LX050724/HFLink/FPGA/src/top.v

`timescale 1 ns / 10 ps

module HFLink_TOP(
        input clk_osc

        ,inout MCU_SWDIO
        ,inout MCU_SWCLK
        // ,input reset

        ,output FLASH_SPI_CSN
        ,input FLASH_SPI_MISO
        ,output FLASH_SPI_MOSI
        ,output FLASH_SPI_CLK
        ,output FLASH_SPI_HOLDN
        ,output FLASH_SPI_WPN

        // 独立串口连接器
        ,output EXT_UART_TX
        ,input EXT_UART_RX

        // SWD/JTAG连接器端口
        ,output EXT_SWCLK_TCK_O
        ,output EXT_SWDIO_TMS_T
        ,output EXT_SWDIO_TMS_O
        ,input EXT_SWDIO_TMS_I
        ,input EXT_SWO_TDO_I
        ,output EXT_TDI_O
        ,input EXT_RTCK_I
        ,input EXT_SRST_I
        ,output EXT_SRST_O
        ,input EXT_TRST_I
        ,output EXT_TRST_O

        // RGB & PWRCTL
        ,output [3:0] GPIO

        // IIC
        ,inout IIC_SDA
        ,inout IIC_SCL

        // USB ULPI
        ,output usb_clk
        ,output usb_rstn
        ,inout [7:0] usb_ulpi_data
        ,input usb_ulpi_nxt
        ,input usb_ulpi_dir
        ,output usb_ulpi_stp
    );

    wire reset = 0;
    wire lock;
    wire clkout0;
    wire clkout1;
    wire clkout2;
    wire n_reset = !reset;
    wire m1_halt;
    wire [3:0] intr;
    assign ready_led = !m1_halt;

    assign FLASH_SPI_HOLDN = 1'd1;
    assign FLASH_SPI_WPN = 1'd1;

    wire [31:0] AHB1HRDATA;
    wire        AHB1HREADYOUT;
    wire [ 1:0] AHB1HRESP;
    wire [ 1:0] AHB1HTRANS;
    wire [ 2:0] AHB1HBURST;
    wire [ 3:0] AHB1HPROT;
    wire [ 2:0] AHB1HSIZE;
    wire        AHB1HWRITE;
    wire        AHB1HREADYMUX;
    wire [ 3:0] AHB1HMASTER;
    wire        AHB1HMASTLOCK;
    wire [31:0] AHB1HADDR;
    wire [31:0] AHB1HWDATA;
    wire        AHB1HSEL;
    wire        AHB1HCLK;
    wire        AHB1HRESET;

    wire [31:0] AHB2HRDATA;
    wire        AHB2HREADYOUT;
    wire [ 1:0] AHB2HRESP;
    wire [ 1:0] AHB2HTRANS;
    wire [ 2:0] AHB2HBURST;
    wire [ 3:0] AHB2HPROT;
    wire [ 2:0] AHB2HSIZE;
    wire        AHB2HWRITE;
    wire        AHB2HREADYMUX;
    wire [ 3:0] AHB2HMASTER;
    wire        AHB2HMASTLOCK;
    wire [31:0] AHB2HADDR;
    wire [31:0] AHB2HWDATA;
    wire        AHB2HSEL;
    wire        AHB2HCLK;
    wire        AHB2HRESET;

    wire [31:0] APB1PADDR;
    wire        APB1PENABLE;
    wire        APB1PWRITE;
    wire [ 3:0] APB1PSTRB;
    wire [ 2:0] APB1PPROT;
    wire [31:0] APB1PWDATA;
    wire        APB1PSEL;
    wire [31:0] APB1PRDATA;
    wire        APB1PREADY;
    wire        APB1PSLVERR;
    wire        APB1PCLK;
    wire        APB1PRESET;

    Gowin_PLL main_pll(
                  .lock(lock), //output lock
                  .clkout0(clkout0), //output clkout0
                  .clkout1(clkout1), //output clkout1
                  .clkout2(clkout2), //output clkout2
                  .clkin(clk_osc), //input clkin
                  .mdclk(clk_osc)
                  //   .reset(reset) //input reset
              );

    wire cm_nreset = n_reset & lock;

    wire MCU_SPI_MOSI;
    wire MCU_SPI_MISO;
    wire MCU_SPI_CLK;
    wire MCU_SPI_CSN;

    Gowin_EMPU_M1_Top Cortex_M1 (
                          //.LOCKUP(lockup), //output LOCKUP
                          .HALTED(m1_halt), //output HALTED
                          .JTAG_7(MCU_SWDIO), //inout JTAG_7
                          .JTAG_9(MCU_SWCLK), //inout JTAG_9
                          .HCLK(clkout0), //input HCLK
                          .hwRstn(cm_nreset), //input hwRstn


                          // AHB1 0x80000000
                          .AHB1HRDATA(AHB1HRDATA), //input [31:0] AHB1HRDATA
                          .AHB1HREADYOUT(AHB1HREADYOUT), //input AHB1HREADYOUT
                          .AHB1HRESP(AHB1HRESP), //input [1:0] AHB1HRESP
                          .AHB1HTRANS(AHB1HTRANS), //output [1:0] AHB1HTRANS
                          .AHB1HBURST(AHB1HBURST), //output [2:0] AHB1HBURST
                          .AHB1HPROT(AHB1HPROT), //output [3:0] AHB1HPROT
                          .AHB1HSIZE(AHB1HSIZE), //output [2:0] AHB1HSIZE
                          .AHB1HWRITE(AHB1HWRITE), //output AHB1HWRITE
                          .AHB1HREADYMUX(AHB1HREADYMUX), //output AHB1HREADYMUX
                          .AHB1HMASTER(AHB1HMASTER), //output [3:0] AHB1HMASTER
                          .AHB1HMASTLOCK(AHB1HMASTLOCK), //output AHB1HMASTLOCK
                          .AHB1HADDR(AHB1HADDR), //output [31:0] AHB1HADDR
                          .AHB1HWDATA(AHB1HWDATA), //output [31:0] AHB1HWDATA
                          .AHB1HSEL(AHB1HSEL), //output AHB1HSEL
                          .AHB1HCLK(AHB1HCLK), //output AHB1HCLK
                          .AHB1HRESET(AHB1HRESET), //output AHB1HRESET

                          // AHB2 0x81000000
                          .AHB2HRDATA(AHB2HRDATA), //input [31:0] AHB2HRDATA
                          .AHB2HREADYOUT(AHB2HREADYOUT), //input AHB2HREADYOUT
                          .AHB2HRESP(AHB2HRESP), //input [1:0] AHB2HRESP
                          .AHB2HTRANS(AHB2HTRANS), //output [1:0] AHB2HTRANS
                          .AHB2HBURST(AHB2HBURST), //output [2:0] AHB2HBURST
                          .AHB2HPROT(AHB2HPROT), //output [3:0] AHB2HPROT
                          .AHB2HSIZE(AHB2HSIZE), //output [2:0] AHB2HSIZE
                          .AHB2HWRITE(AHB2HWRITE), //output AHB2HWRITE
                          .AHB2HREADYMUX(AHB2HREADYMUX), //output AHB2HREADYMUX
                          .AHB2HMASTER(AHB2HMASTER), //output [3:0] AHB2HMASTER
                          .AHB2HMASTLOCK(AHB2HMASTLOCK), //output AHB2HMASTLOCK
                          .AHB2HADDR(AHB2HADDR), //output [31:0] AHB2HADDR
                          .AHB2HWDATA(AHB2HWDATA), //output [31:0] AHB2HWDATA
                          .AHB2HSEL(AHB2HSEL), //output AHB2HSEL
                          .AHB2HCLK(AHB2HCLK), //output AHB2HCLK
                          .AHB2HRESET(AHB2HRESET), //output AHB2HRESET

                          // APB1 0x60000000
                          .APB1PADDR(APB1PADDR), //output [31:0] APB1PADDR
                          .APB1PENABLE(APB1PENABLE), //output APB1PENABLE
                          .APB1PWRITE(APB1PWRITE), //output APB1PWRITE
                          .APB1PSTRB(APB1PSTRB), //output [3:0] APB1PSTRB
                          .APB1PPROT(APB1PPROT), //output [2:0] APB1PPROT
                          .APB1PWDATA(APB1PWDATA), //output [31:0] APB1PWDATA
                          .APB1PSEL(APB1PSEL), //output APB1PSEL
                          .APB1PRDATA(APB1PRDATA), //input [31:0] APB1PRDATA
                          .APB1PREADY(APB1PREADY), //input APB1PREADY
                          .APB1PSLVERR(APB1PSLVERR), //input APB1PSLVERR
                          .APB1PCLK(APB1PCLK), //output APB1PCLK
                          .APB1PRESET(APB1PRESET), //output APB1PRESET

                          // SPI
                          .MOSI(MCU_SPI_MOSI), //output MOSI
                          .MISO(MCU_SPI_MISO), //input MISO
                          .SCLK(MCU_SPI_CLK), //output SCLK
                          .NSS(MCU_SPI_CSN), //output NSS

                          // IIC
                          .SDA(IIC_SDA),
                          .SCL(IIC_SCL),

                          .EXTINT(intr) //input [3:0] EXTINT
                      );

    wire [7:0] usb_ulpi_data_i;
    wire [7:0] usb_ulpi_data_o;

    wire winusb_out_tready;
    wire winusb_out_tvalid;
    wire [7:0] winusb_out_tdata;
    wire cdc_in_tvalid;
    wire [7:0] cdc_in_tdata;
    wire cdc_out_tready;
    wire cdc_out_tvalid;
    wire [7:0] cdc_out_tdata;

    wire [3:0] ext_usb_endpt;
    wire ext_usb_txact;
    wire ext_usb_txpop;
    wire ext_usb_txpktfin;
    wire ext_usb_txcork;
    wire [7:0] ext_usb_txdata;
    wire [11:0] ext_usb_txlen;
    wire [7:0] ext_usb_rxdat;
    wire ext_usb_rxval;
    wire ext_usb_rxrdy;
    wire ext_usb_rxact;
    wire ext_usb_rxpktval;


    AHB_USBDevice u_usb0 (
                      .hclk(AHB1HCLK),
                      .hresetn(AHB1HRESET),
                      .hsels(AHB1HSEL),
                      .haddrs(AHB1HADDR[11:0]),
                      .htranss(AHB1HTRANS),
                      .hsizes(AHB1HSIZE),
                      .hwrites(AHB1HWRITE),
                      .hreadys(AHB1HREADYMUX),
                      .hwdatas(AHB1HWDATA),
                      .hreadyouts(AHB1HREADYOUT),
                      .hresps(AHB1HRESP[0]),
                      .hrdatas(AHB1HRDATA),
                      .intr(intr[0]),
                      .usb_ulpi_data_i(usb_ulpi_data_i),
                      .usb_ulpi_data_o(usb_ulpi_data_o),
                      .usb_ulpi_data(usb_ulpi_data),
                      .usb_ulpi_nxt(usb_ulpi_nxt),
                      .usb_ulpi_dir(usb_ulpi_dir),
                      .usb_ulpi_stp(usb_ulpi_stp),
                      .usb_nrst(usb_rstn),

                      .ext_usb_endpt(ext_usb_endpt),
                      .ext_usb_txact(ext_usb_txact),
                      .ext_usb_txpop(ext_usb_txpop),
                      .ext_usb_txpktfin(ext_usb_txpktfin),
                      .ext_usb_txcork(ext_usb_txcork),
                      .ext_usb_txdata(ext_usb_txdata),
                      .ext_usb_txlen(ext_usb_txlen),
                      .ext_usb_rxdat(ext_usb_rxdat),
                      .ext_usb_rxval(ext_usb_rxval),
                      .ext_usb_rxrdy(ext_usb_rxrdy),
                      .ext_usb_rxact(ext_usb_rxact),
                      .ext_usb_rxpktval(ext_usb_rxpktval),

                      .cdc_in_tvalid(cdc_in_tvalid),
                      .cdc_in_tdata(cdc_in_tdata),
                      .cdc_out_tready(cdc_out_tready),
                      .cdc_out_tvalid(cdc_out_tvalid),
                      .cdc_out_tdata(cdc_out_tdata)
                  );
    assign usb_clk = AHB1HCLK;

    genvar i;
    generate
        for(i = 0; i < 8; i = i + 1) begin: io_genfor
            IOBUF usb_data_io_u(
                      .O(usb_ulpi_data_i[i]),
                      .I(usb_ulpi_data_o[i]),
                      .IO(usb_ulpi_data[i]),
                      .OEN(usb_ulpi_dir)
                  );
        end
    endgenerate

    wire LOC_UART_TX;
    wire LOC_UART_RX;

    // ── UART ↔ USB CDC 桥接 (DAP_USB_Receiver / DAP_USB_Transfer) ──
    wire        cdc_txcork, cdc_rxrdy;
    wire [7:0]  cdc_txdata;
    wire [11:0] cdc_txlen;
    wire        uart_tx_tvalid;
    wire        uart_tx_tready;
    wire [7:0]  uart_tx_tdata;
    wire        uart_rx_tvalid;
    wire [7:0]  uart_rx_tdata;
    wire        uart_rx_fifo_clear;
    wire        uart_rx_fifo_clear_done;
    wire        uart_tx_fifo_clear;
    wire        uart_tx_fifo_clear_done;

    // CDC OUT (EP4, host→device): USB RX → AXIS → UART TX
    DAP_USB_Receiver #(
        .P_ENDPOINT(4'd4),
        .FIFO_DEPTH(1024),
        .FIFO_BUFFER_LEN(512)
    ) cdc_usb_receiver (
        .clk(AHB1HCLK),
        .resetn(AHB1HRESET),

        .clear_data(uart_tx_fifo_clear),
        .clear_done(uart_tx_fifo_clear_done),

        .usb_endpt(ext_usb_endpt),
        .usb_rxval(ext_usb_rxval),
        .usb_rxdat(ext_usb_rxdat),
        .usb_rxpktval(ext_usb_rxpktval),
        .usb_rxact(ext_usb_rxact),
        .usb_rxrdy(cdc_rxrdy),

        .fifo_full(),
        .fifo_empty(),

        .axis_tvaild(uart_tx_tvalid),
        .axis_tdata(uart_tx_tdata),
        .axis_tready(uart_tx_tready)
    );

    // UART RX → AXIS → USB TX → CDC IN (EP3, device→host)
    DAP_USB_Transfer #(
        .P_ENDPOINT(4'd3),
        .FIFO_DEPTH(1024),
        .FIFO_BUFFER_LEN(512)
    ) cdc_usb_transfer (
        .clk(AHB1HCLK),
        .resetn(AHB1HRESET),

        .clear_data(uart_rx_fifo_clear),
        .clear_done(uart_rx_fifo_clear_done),

        .in_tvalid(uart_rx_tvalid),
        .in_tready(),
        .in_tdata(uart_rx_tdata),

        .fifo_size(),

        .usb_endpt(ext_usb_endpt),
        .usb_txact(ext_usb_txact),
        .usb_txpop(ext_usb_txpop),
        .usb_txpktfin(ext_usb_txpktfin),
        .usb_txcork(cdc_txcork),
        .usb_txdata(cdc_txdata),
        .usb_txlen(cdc_txlen)
    );

    // ── APB_Stream_UART (保留 APB 配置 + UART 物理层) ──
    APB_Stream_UART apb_stream_uart(
                        // APB
                        .PCLK(APB1PCLK),
                        .PWRITE(APB1PWRITE),
                        .PSEL(APB1PSEL),
                        .PENABLE(APB1PENABLE),
                        .PADDR(APB1PADDR),
                        .PSTRB(APB1PSTRB),
                        .PWDATA(APB1PWDATA),
                        .PRDATA(APB1PRDATA),
                        .PREADY(APB1PREADY),
                        .PRESETn(APB1PRESET),

                        .rx_fifo_clear(uart_rx_fifo_clear),
                        .rx_fifo_clear_done(uart_rx_fifo_clear_done),
                        .tx_fifo_clear(uart_tx_fifo_clear),
                        .tx_fifo_clear_done(uart_tx_fifo_clear_done),

                        // Data Stream (经 DAP 模块桥接)
                        .tx_tvalid(uart_tx_tvalid),
                        .tx_tready(uart_tx_tready),
                        .tx_tdata(uart_tx_tdata),
                        .rx_tvalid(uart_rx_tvalid),
                        .rx_tdata(uart_rx_tdata),

                        // UART IO
                        .UART_TX(LOC_UART_TX),
                        .UART_RX(LOC_UART_RX)
                    );

    // ── 原内部 CDC 路径 (usb_fifo) 已移除，端口接地 ──
    assign cdc_in_tvalid = 1'b0;
    assign cdc_in_tdata  = 8'd0;
    assign cdc_out_tready = 1'b0;

    wire LOC_SPI_MUX;
    wire LOC_SPI_MISO;

    // ── USB TX/RX 多路复用: DAP_Controller ↔ CDC 桥接 ──
    wire        dap_txcork, dap_rxrdy;
    wire [7:0]  dap_txdata;
    wire [11:0] dap_txlen;

    DAP_Controller dap_controller_inst(
                       .hclk(AHB2HCLK),
                       .hresetn(AHB2HRESET),
                       .hsels(AHB2HSEL),
                       .haddrs(AHB2HADDR[11:0]),
                       .htranss(AHB2HTRANS),
                       .hsizes(AHB2HSIZE),
                       .hwrites(AHB2HWRITE),
                       .hreadys(AHB2HREADYMUX),
                       .hwdatas(AHB2HWDATA),
                       .hreadyouts(AHB2HREADYOUT),
                       .hresps(AHB2HRESP[0]),
                       .hrdatas(AHB2HRDATA),

                       .sclk(clkout1),
                       .clk_200M(clkout2),

                       .usb_endpt(ext_usb_endpt),
                       .usb_txact(ext_usb_txact),
                       .usb_txpop(ext_usb_txpop),
                       .usb_txpktfin(ext_usb_txpktfin),
                       .usb_txcork(dap_txcork),
                       .usb_txdata(dap_txdata),
                       .usb_txlen(dap_txlen),
                       .usb_rxdat(ext_usb_rxdat),
                       .usb_rxval(ext_usb_rxval),
                       .usb_rxrdy(dap_rxrdy),
                       .usb_rxact(ext_usb_rxact),
                       .usb_rxpktval(ext_usb_rxpktval),

                       .intr(intr[1]),

                       .EXT_SWCLK_TCK_O(EXT_SWCLK_TCK_O),
                       .EXT_SWDIO_TMS_T(EXT_SWDIO_TMS_T),
                       .EXT_SWDIO_TMS_O(EXT_SWDIO_TMS_O),
                       .EXT_SWDIO_TMS_I(EXT_SWDIO_TMS_I),
                       .EXT_SWO_TDO_I(EXT_SWO_TDO_I),
                       .EXT_TDI_O(EXT_TDI_O),
                       .EXT_RTCK_I(EXT_RTCK_I),
                       .EXT_SRST_I(EXT_SRST_I),
                       .EXT_SRST_O(EXT_SRST_O),
                       .EXT_TRST_I(EXT_TRST_I),
                       .EXT_TRST_O(EXT_TRST_O),
                       .EXT_UART_TX(EXT_UART_TX),
                       .EXT_UART_RX(EXT_UART_RX),

                       .LOC_UART_TX(LOC_UART_TX),
                       .LOC_UART_RX(LOC_UART_RX),

                       .LOC_SPI_CSN(MCU_SPI_CSN),
                       .LOC_SPI_MISO(LOC_SPI_MISO),
                       .LOC_SPI_MOSI(MCU_SPI_MOSI),
                       .LOC_SPI_CLK(MCU_SPI_CLK),
                       .LOC_SPI_MUX(LOC_SPI_MUX),
                       .DAP_GPIO(GPIO)
                   );

    // ── 外部 USB TX/RX 多路复用 ──
    assign ext_usb_txcork = (ext_usb_endpt == 4'd3) ? cdc_txcork : dap_txcork;
    assign ext_usb_txdata = (ext_usb_endpt == 4'd3) ? cdc_txdata : dap_txdata;
    assign ext_usb_txlen  = (ext_usb_endpt == 4'd3) ? cdc_txlen  : dap_txlen;
    assign ext_usb_rxrdy  = (ext_usb_endpt == 4'd4) ? cdc_rxrdy : dap_rxrdy;

    assign MCU_SPI_MISO = LOC_SPI_MUX ? LOC_SPI_MISO : FLASH_SPI_MISO;
    assign FLASH_SPI_CSN = LOC_SPI_MUX ? 1'd1 : MCU_SPI_CSN;
    assign FLASH_SPI_MOSI = LOC_SPI_MUX ? 1'd0 : MCU_SPI_MOSI;
    assign FLASH_SPI_CLK = LOC_SPI_MUX ? 1'd0 : MCU_SPI_CLK;
endmodule
