LX050724/HFLink/FPGA/src/USB_desc.v

`timescale 1 ns / 10 ps

module USB_DESC#(
        parameter ADDRWIDTH = 12,
        parameter [ADDRWIDTH-1:0] BASE_ADDR = 0
    ) (
        input clk,
        input resetn,
        input usbrst,

        // AHB MEM接口
        input ahb_write_en,
        input ahb_read_en,
        input [ADDRWIDTH-1:0] ahb_addr,
        output reg [31:0] ahb_rdata,
        input [31:0] ahb_wdata,
        input [3:0] ahb_byte_strobe,

        output [7:0] txdat,
        output reg txval,
        output reg [11:0] txdat_len,
        input txpop,
        input txact,
        input [7:0] rxdat,
        input rxval,
        output reg rxrdy,
        input rxact,
        input setup,
        input [3:0] endpt_sel,

        input [15:0] descrom_raddr,
        input [7:0] desc_index,
        input [7:0] desc_type,
        output [7:0] descrom_rdata,
        output [15:0] desc_dev_addr,
        output [15:0] desc_dev_len,
        output [15:0] desc_qual_addr,
        output [15:0] desc_qual_len,
        output [15:0] desc_fscfg_addr,
        output [15:0] desc_fscfg_len,
        output [15:0] desc_hscfg_addr,
        output [15:0] desc_hscfg_len,
        output [15:0] desc_oscfg_addr,
        output [15:0] desc_hidrpt_addr,
        output [15:0] desc_hidrpt_len,
        output [15:0] desc_bos_addr,
        output [15:0] desc_bos_len,
        output [15:0] desc_strlang_addr,
        output [15:0] desc_strvendor_addr,
        output [15:0] desc_strvendor_len,
        output [15:0] desc_strproduct_addr,
        output [15:0] desc_strproduct_len,
        output [15:0] desc_strserial_addr,
        output [15:0] desc_strserial_len,
        output desc_have_strings,

        output reg intr
    );

    localparam [ADDRWIDTH-1:0] USB_SETUP_DATA_ADDR  = 12'h000 + BASE_ADDR; // 8B RO
    localparam [ADDRWIDTH-1:0] CDC_LINE_CODE_ADDR   = 12'h008 + BASE_ADDR; // 6+2B RO
    localparam [ADDRWIDTH-1:0] SERIAL_DESC_ADDR     = 12'h010 + BASE_ADDR; // 68B RW


    reg [7:0] desc_rom [0:503];

    assign desc_dev_addr = 16'd10;
    assign desc_dev_len = 16'd18;
    assign desc_qual_addr = 16'd0;
    assign desc_qual_len = 16'd10;
    assign desc_fscfg_addr = 16'd133;
    assign desc_fscfg_len = 16'd105;
    assign desc_hscfg_addr = 16'd28;
    assign desc_hscfg_len = 16'd105;
    assign desc_oscfg_addr = 16'd238;
    assign desc_hidrpt_addr = 16'd0;
    assign desc_hidrpt_len = 16'd0;
    assign desc_bos_addr = 16'd409;
    assign desc_bos_len = 16'd33;
    assign desc_strlang_addr = 16'd442;
    assign desc_strvendor_addr = 16'd446;
    assign desc_strvendor_len = 16'd14;
    assign desc_strproduct_addr = 16'd460;
    assign desc_strproduct_len = 16'd44;
    assign desc_strserial_addr = 16'h8000;
    assign desc_strserial_len = 16'd66;
    assign desc_have_strings = 1'd1;

    localparam [15:0] desc_winusb_addr = 16'd239;
    localparam [15:0] desc_winusb_len = 16'd170;


    integer i;
    genvar gi;
    reg [31:0] serial_str_ram_word [0:16];

    wire [7:0] serial_str_ram [0:67];

    generate
        for (gi = 0; gi < 68; gi=gi+1) begin
            assign serial_str_ram[gi] = serial_str_ram_word[gi/4][(gi%4)*8+:8];
        end
    endgenerate


    reg [7:0] txdat_reg;
    reg desc_mode;
    reg [15:0] desc_manual_raddr;
    reg [15:0] desc_other_str_addr;

    wire usb_rx_active = endpt_sel == 4'd0 && rxact;
    wire usb_tx_active = endpt_sel == 4'd0 && txact;
    wire rst = !resetn || usbrst;

    wire [15:0] desc_rom_raddr = desc_mode ? desc_manual_raddr : descrom_raddr;
    assign descrom_rdata = desc_rom_raddr[15] ? serial_str_ram[desc_rom_raddr[6:0]] : desc_rom[desc_rom_raddr];
    assign txdat = desc_mode ? descrom_rdata : txdat_reg;

    reg [7:0] setup_data [0:7];
    reg [7:0] line_coding [0:6];

    wire [7:0] bmRequestType = setup_data[0];
    wire [7:0] bRequest = setup_data[1];
    wire [15:0] wValue = {setup_data[3], setup_data[2]};
    wire [15:0] wIndex = {setup_data[5], setup_data[4]};
    wire [15:0] wLength = {setup_data[7], setup_data[6]};


    localparam [2:0] IDLE = 3'd0;
    localparam [2:0] PARSE_REQUEST = 3'd1;
    localparam [2:0] SEND_WINUSB_DESC = 3'd2;
    localparam [2:0] SEND_WINUSB_DESC_TURN = 3'd3;
    localparam [2:0] GET_LINE_CODING = 3'd4;
    localparam [2:0] SET_LINE_CODING = 3'd5;

    localparam [7:0] CDC_REQUEST_SET_LINE_CODING = 8'h20;
    localparam [7:0] CDC_REQUEST_GET_LINE_CODING = 8'h21;
    localparam [7:0] CDC_REQUEST_SET_CONTROL_LINE_STATE = 8'h22;
    localparam [7:0] CDC_REQUEST_SEND_BREAK = 8'h23;

    reg [2:0] setup_sm;
    reg [2:0] rx_byte_cnt;
    reg [5:0] tx_byte_cnt;
    reg [7:0] tx_num;


    always @(posedge clk or negedge resetn) begin
        if (!resetn) begin
            setup_sm <= IDLE;
            rx_byte_cnt <= 0;
            tx_byte_cnt <= 0;
            txdat_reg <= 0;
            txdat_len <= 0;
            rxrdy <= 1'd0;
            txval <= 1'd0;
            desc_mode <= 0;
            desc_manual_raddr <= 0;
            desc_other_str_addr <= 0;
            intr <= 0;
            tx_num <= 0;

            for (i = 0; i < 8; i=i+1) begin
                setup_data[i] <= 8'd0;
            end
            for (i = 0; i < 6; i=i+1) begin
                line_coding[i] <= 8'd0;
            end
        end
        else begin
            if (ahb_write_en) begin
                case (ahb_addr[ADDRWIDTH-1:2])
                    CDC_LINE_CODE_ADDR[ADDRWIDTH-1:2]: begin
                        if (ahb_byte_strobe[0]) begin
                            line_coding[0] <= ahb_wdata[7:0];
                        end
                        if (ahb_byte_strobe[0]) begin
                            line_coding[1] <= ahb_wdata[15:8];
                        end
                        if (ahb_byte_strobe[1]) begin
                            line_coding[2] <= ahb_wdata[23:16];
                        end
                        if (ahb_byte_strobe[2]) begin
                            line_coding[3] <= ahb_wdata[31:24];
                        end
                    end
                    CDC_LINE_CODE_ADDR[ADDRWIDTH-1:2]+1: begin
                        if (ahb_byte_strobe[0]) begin
                            line_coding[4] <= ahb_wdata[7:0];
                        end
                        if (ahb_byte_strobe[1]) begin
                            line_coding[5] <= ahb_wdata[15:8];
                        end
                        if (ahb_byte_strobe[2]) begin
                            line_coding[6] <= ahb_wdata[23:16];
                        end
                    end
                endcase
            end

            case (setup_sm)
                IDLE: begin
                    if (setup) begin
                        if (rxval) begin
                            setup_data[rx_byte_cnt] <= rxdat;
                            rx_byte_cnt <= rx_byte_cnt + 1;
                            if (rx_byte_cnt == 3'd7) begin
                                setup_sm <= PARSE_REQUEST;
                            end
                        end
                    end
                    else begin
                        rx_byte_cnt <= 3'd0;
                    end
                end
                PARSE_REQUEST: begin  // 判断请求类型
                    if (bmRequestType[6:5] == 2'd0 && bmRequestType[1:0] == 2'd0 && bRequest == 8'h06 && wValue[15:8] == 8'h03) begin
                        // TODO 支持更多字符串描述符
                        setup_sm <= IDLE;  // 字符串描述符请求
                    end
                    else if (bmRequestType[6:5] == 2'd1 && bmRequestType[1:0] == 2'd1 && wIndex[7:0] == 16'd1) begin
                        case (bRequest)
                            CDC_REQUEST_SET_LINE_CODING: begin
                                setup_sm <= SET_LINE_CODING;
                            end
                            CDC_REQUEST_GET_LINE_CODING: begin
                                setup_sm <= GET_LINE_CODING;
                            end
                            CDC_REQUEST_SET_CONTROL_LINE_STATE: begin
                                intr <= 1'd1;
                                setup_sm <= IDLE;
                            end
                            CDC_REQUEST_SEND_BREAK: begin
                                intr <= 1'd1;
                                setup_sm <= IDLE;
                            end
                            default: begin
                                setup_sm <= IDLE;
                            end
                        endcase
                    end
                    else if (bmRequestType[6:5] == 2'd2 && bRequest == 8'h20 && wIndex == 16'h07) begin
                        // WINUSB供应商请求
                        tx_num <= desc_winusb_len;
                        desc_manual_raddr <= desc_winusb_addr;
                        desc_mode <= 1'd1;
                        setup_sm <= SEND_WINUSB_DESC;
                    end
                    else begin
                        setup_sm <= IDLE;  // 默认处理无效请求
                    end
                end
                SEND_WINUSB_DESC: begin
                    if (usb_tx_active) begin
                        if (txpop) begin
                            tx_byte_cnt <= tx_byte_cnt + 1;
                            desc_manual_raddr <= desc_manual_raddr + 1;
                        end

                        if (tx_byte_cnt == 6'd63) begin
                            txval <= 1'd0;
                            tx_num <= tx_num - 8'd64;
                            setup_sm <= SEND_WINUSB_DESC_TURN;
                        end

                        if (tx_byte_cnt + 1'd1 == tx_num) begin
                            txval <= 1'd0;
                            tx_num <= 8'd0;
                            desc_mode <= 0;
                            setup_sm <= IDLE;
                        end
                    end
                    else begin
                        txdat_len <= tx_num > 64 ? 64 : tx_num;
                        tx_byte_cnt <= 6'd0;
                        txval <= 1'd1;
                    end
                end
                SEND_WINUSB_DESC_TURN: begin
                    if (!usb_tx_active) begin
                        setup_sm <= SEND_WINUSB_DESC;
                    end
                end
                GET_LINE_CODING: begin
                    txdat_len <= 12'd7;
                    txval <= 1'd1;
                    if (usb_tx_active) begin
                        if (txpop) begin
                            tx_byte_cnt <= tx_byte_cnt + 1;
                            txdat_reg <= line_coding[tx_byte_cnt + 1];
                            if (tx_byte_cnt == 6'd6) begin
                                txval <= 1'd0;
                                setup_sm <= IDLE;
                            end
                        end
                    end
                    else begin
                        tx_byte_cnt <= 6'd0;
                        txdat_reg <= line_coding[0];
                    end
                end
                SET_LINE_CODING: begin
                    rxrdy <= 1'd1;
                    if (usb_rx_active) begin
                        if (rxval) begin
                            rx_byte_cnt <= rx_byte_cnt + 1;
                            line_coding[rx_byte_cnt] <= rxdat;
                            if (rx_byte_cnt == 3'd6) begin
                                intr <= 1'd1; // 接收linecoding后触发中断
                                setup_sm <= IDLE;
                            end
                        end
                    end
                    else begin
                        rx_byte_cnt <= 3'd0;
                    end
                end
                default: begin
                    setup_sm <= IDLE;  // 安全默认
                end
            endcase

            if (usbrst) begin
                setup_sm <= IDLE;
            end

            if (ahb_read_en && ahb_addr[ADDRWIDTH-1:2] == USB_SETUP_DATA_ADDR[ADDRWIDTH-1:2]) begin
                intr <= 1'd0;
            end
        end
    end

    always @(posedge clk or negedge resetn) begin
        if (!resetn) begin
            for (i = 0; i < 17; i=i+1) begin
                serial_str_ram_word[i] <= 32'd0;
            end
        end
        else begin
            if (ahb_write_en) begin
                if (ahb_addr[ADDRWIDTH-1:2] >= SERIAL_DESC_ADDR[ADDRWIDTH-1:2] && ahb_addr[ADDRWIDTH-1:2] < (SERIAL_DESC_ADDR[ADDRWIDTH-1:2] + 5'd17)) begin
                    if (ahb_byte_strobe[0]) begin
                        serial_str_ram_word[ahb_addr[ADDRWIDTH-1:2]-SERIAL_DESC_ADDR[ADDRWIDTH-1:2]][7:0] <= ahb_wdata[7:0];
                    end
                    if (ahb_byte_strobe[1]) begin
                        serial_str_ram_word[ahb_addr[ADDRWIDTH-1:2]-SERIAL_DESC_ADDR[ADDRWIDTH-1:2]][15:8] <= ahb_wdata[15:8];
                    end
                    if (ahb_byte_strobe[2]) begin
                        serial_str_ram_word[ahb_addr[ADDRWIDTH-1:2]-SERIAL_DESC_ADDR[ADDRWIDTH-1:2]][23:16] <= ahb_wdata[23:16];
                    end
                    if (ahb_byte_strobe[3]) begin
                        serial_str_ram_word[ahb_addr[ADDRWIDTH-1:2]-SERIAL_DESC_ADDR[ADDRWIDTH-1:2]][31:24] <= ahb_wdata[31:24];
                    end
                end
            end
        end
    end

    always @(*) begin
        if (ahb_read_en) begin
            case (ahb_addr[ADDRWIDTH-1:2])
                USB_SETUP_DATA_ADDR[ADDRWIDTH-1:2]: begin
                    ahb_rdata = {setup_data[3], setup_data[2], setup_data[1], setup_data[0]};
                end
                USB_SETUP_DATA_ADDR[ADDRWIDTH-1:2] + 1: begin
                    ahb_rdata = {setup_data[7], setup_data[6], setup_data[5], setup_data[4]};
                end
                CDC_LINE_CODE_ADDR[ADDRWIDTH-1:2]: begin
                    ahb_rdata = {line_coding[3], line_coding[2], line_coding[1], line_coding[0]};
                end
                CDC_LINE_CODE_ADDR[ADDRWIDTH-1:2] + 1: begin
                    ahb_rdata = {8'h00, line_coding[6], line_coding[5], line_coding[4]};
                end
                SERIAL_DESC_ADDR[ADDRWIDTH-1:2]+5'h00,
                SERIAL_DESC_ADDR[ADDRWIDTH-1:2]+5'h01,
                SERIAL_DESC_ADDR[ADDRWIDTH-1:2]+5'h02,
                SERIAL_DESC_ADDR[ADDRWIDTH-1:2]+5'h03,
                SERIAL_DESC_ADDR[ADDRWIDTH-1:2]+5'h04,
                SERIAL_DESC_ADDR[ADDRWIDTH-1:2]+5'h05,
                SERIAL_DESC_ADDR[ADDRWIDTH-1:2]+5'h06,
                SERIAL_DESC_ADDR[ADDRWIDTH-1:2]+5'h07,
                SERIAL_DESC_ADDR[ADDRWIDTH-1:2]+5'h08,
                SERIAL_DESC_ADDR[ADDRWIDTH-1:2]+5'h09,
                SERIAL_DESC_ADDR[ADDRWIDTH-1:2]+5'h0A,
                SERIAL_DESC_ADDR[ADDRWIDTH-1:2]+5'h0B,
                SERIAL_DESC_ADDR[ADDRWIDTH-1:2]+5'h0C,
                SERIAL_DESC_ADDR[ADDRWIDTH-1:2]+5'h0D,
                SERIAL_DESC_ADDR[ADDRWIDTH-1:2]+5'h0E,
                SERIAL_DESC_ADDR[ADDRWIDTH-1:2]+5'h0F,
                SERIAL_DESC_ADDR[ADDRWIDTH-1:2]+5'h10,
                SERIAL_DESC_ADDR[ADDRWIDTH-1:2]+5'h11 : begin
                    ahb_rdata = serial_str_ram_word[ahb_addr[ADDRWIDTH-1:2]-SERIAL_DESC_ADDR[ADDRWIDTH-1:2]];
                end
                default: begin
                    ahb_rdata = 32'hxxxx_xxxx;
                end
            endcase
        end
        else begin
            ahb_rdata = 32'hxxxx_xxxx;
        end
    end

    initial begin
        desc_rom[  0] = 8'h0a;
        desc_rom[  1] = 8'h06;
        desc_rom[  2] = 8'h10;
        desc_rom[  3] = 8'h02;
        desc_rom[  4] = 8'h00;
        desc_rom[  5] = 8'h00;
        desc_rom[  6] = 8'h00;
        desc_rom[  7] = 8'h40;
        desc_rom[  8] = 8'h01;
        desc_rom[  9] = 8'h00;
        desc_rom[ 10] = 8'h12;
        desc_rom[ 11] = 8'h01;
        desc_rom[ 12] = 8'h10;
        desc_rom[ 13] = 8'h02;
        desc_rom[ 14] = 8'hef;
        desc_rom[ 15] = 8'h02;
        desc_rom[ 16] = 8'h01;
        desc_rom[ 17] = 8'h40;
        desc_rom[ 18] = 8'h28;
        desc_rom[ 19] = 8'h0d;
        desc_rom[ 20] = 8'h04;
        desc_rom[ 21] = 8'h02;
        desc_rom[ 22] = 8'h00;
        desc_rom[ 23] = 8'h01;
        desc_rom[ 24] = 8'h01;
        desc_rom[ 25] = 8'h02;
        desc_rom[ 26] = 8'h03;
        desc_rom[ 27] = 8'h01;
        desc_rom[ 28] = 8'h09;
        desc_rom[ 29] = 8'h02;
        desc_rom[ 30] = 8'h69;
        desc_rom[ 31] = 8'h00;
        desc_rom[ 32] = 8'h03;
        desc_rom[ 33] = 8'h01;
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
        desc_rom[495] = 8'h00;
        desc_rom[496] = 8'h50;
        desc_rom[497] = 8'h00;
        desc_rom[498] = 8'h6c;
        desc_rom[499] = 8'h00;
        desc_rom[500] = 8'h75;
        desc_rom[501] = 8'h00;
        desc_rom[502] = 8'h73;
        desc_rom[503] = 8'h00;
    end

endmodule
