LX050724/HFLink/FPGA/testbench/DAP_SWD_Trans_tb/DAP_SWD_Trans_tb.v

`timescale 1 ns/ 10 ps
`include "DAP_Cmd.v"

`define DELAY_TIME 20
`define TRUN_CYCLE 12'd0

module DAP_SWD_Trans_tb();
    reg clk;
    reg clk_x2;
    reg resetn;
    integer i;

    reg [7:0] test_data [0:4095];

    initial begin
        $dumpfile("test.vcd");
        $dumpvars(0, DAP_SWD_Trans_tb);
        $readmemh("test_data.txt", test_data);

        clk = 0;
        clk_x2 = 0;
        resetn = 1;
        #2
         resetn = 0;
        #8;
        resetn = 1;

        forever begin
            clk_x2 <= 1;
            #(8.333333/2);
            clk_x2 <= 0;
            #(8.333333/2);
            clk <= !clk;
        end
    end



    reg ahb_write_en;
    reg ahb_read_en;
    reg [11:0] ahb_addr;
    reg [31:0] ahb_wdata;
    reg [3:0] ahb_byte_strobe;
    reg [`CMD_REAL_NUM-1:0] start;
    wire [`CMD_REAL_NUM-1:0] done;
    reg wait_status = 0;
    wire read_en = dap_in_tready & start ? 1'd1 : (cnt > 5 && wait_status == 0);

    assign done[1:0] = 0;

    reg [31:0] cnt;
    always @(posedge clk or negedge resetn) begin
        if (!resetn) begin
            cnt <= 0;
            ahb_write_en <= 0;
            ahb_read_en <= 0;
            ahb_addr <= 0;
            ahb_wdata <= 0;
            ahb_byte_strobe <= 0;
            start <= 0;
        end
        else begin
            cnt <= cnt + 1;
            ahb_write_en <= 0;
            ahb_read_en <= 0;

            case (cnt)
                0: begin
                    // BAUD_TIMING
                    ahb_write_en <= 1;
                    ahb_addr <= 12'h004;
                    // ahb_wdata <= 32'h0001_0001;
                    ahb_wdata <= 32'h0002_0002;
                    ahb_byte_strobe <= 4'hf;
                end
                1: begin
                    // SWJ_RETRY
                    ahb_write_en <= 1;
                    ahb_addr <= 12'h080 + 12'h004;
                    ahb_wdata <= 32'h0004_0004;
                    ahb_byte_strobe <= 4'hf;
                end
                2: begin
                    // SWJ_CR
                    ahb_write_en <= 1;
                    ahb_addr <= 12'h080 + 12'h000;
                    ahb_wdata <= 32'h0000_0000;
                    ahb_byte_strobe <= 4'hf;
                end
                3: begin
                    // SWJ_SWD_CR
                    ahb_write_en <= 1;
                    ahb_addr <= 12'h080 + 12'h008;
                    // ahb_wdata <= {1'd0, 1'd0, 2'd2};
                    ahb_wdata <= {1'd1, 1'd0, 2'd0};
                    ahb_byte_strobe <= 4'hf;
                end
                4: begin
                    // BAUD_CR
                    ahb_write_en <= 1;
                    ahb_addr <= 12'h000;
                    // ahb_wdata <= 32'h0002_0001;
                    ahb_wdata <= 32'h0000_0001;
                    ahb_byte_strobe <= 4'hf;
                end

            endcase

            if (cnt == 32'h0001_0000) begin
                $finish(1);
            end
        end
    end

    always @(posedge clk) begin
        if (cnt == 5) begin
            $display("start test");
        end
        else if (cnt > 5) begin
            if (wait_status == 0) begin
                wait_status <= 1'd1;
                $display("===============================================");
                case (dap_in_tdata)
                    8'h05: begin
                        $display("TEST: DAP_Transfer");
                        start[`CMD_TRANSFER_SHIFT] <= 1'd1;
                    end
                    8'h06: begin
                        $display("TEST: DAP_TransferBlock");
                        start[`CMD_TRANSFER_BLOCK_SHIFT] <= 1'd1;
                    end
                    8'h12: begin
                        $display("TEST: DAP_SWJ_Seqence");
                        start[`CMD_SWJ_SEQUENCE_SHIFT] <= 1'd1;
                    end
                    8'h1d: begin
                        $display("TEST: DAP_SWD_Seqence");
                        start[`CMD_SWD_SEQUENCE_SHIFT] <= 1'd1;
                    end
                    8'hff: begin
                        $display("end test");
                        $finish(1);
                    end
                    default: begin
                        $display("unknown cmd %02x", dap_in_tdata);
                        $finish(1);
                    end
                endcase
            end
            else begin
                if (done[9:0] != 0) begin
                    start <= 0;
                    wait_status <= 0;
                    swd_sm <= 0;
                    #1
                    $display("packet_len: %d", packet_len);
                    for (i = 0; i < packet_len; i = i + 1) begin
                        $display("%08x: %02x", i, output_data[i]);
                    end
                end
            end
        end
    end

    reg [11:0] ram_address;
    reg dap_in_tvalid;
    wire [`CMD_REAL_NUM-1:0] dap_in_tready;
    wire [7:0] dap_in_tdata = test_data[ram_address];
    reg [31:0] timestamp;
    always @(posedge clk or negedge resetn) begin
        if (!resetn) begin
            ram_address <= 0;
            dap_in_tvalid <= 0;
            timestamp <= 0;
        end
        else begin
            timestamp <= timestamp + 1;
            dap_in_tvalid <= 1;
            if (read_en)
                ram_address <= ram_address + 1;
        end
    end


    wire sclk_negedge;
    wire sclk_sampling;
    wire sclk_out;
    wire sclk_sampling_en;

    DAP_BaudGenerator baud_inst(
                          .clk(clk),
                          .sclk_in(clk_x2),
                          .resetn(resetn),

                          .ahb_write_en(ahb_write_en),
                          .ahb_read_en(ahb_read_en),
                          .ahb_addr(ahb_addr),
                          .ahb_rdata(),
                          .ahb_wdata(ahb_wdata),
                          .ahb_byte_strobe(ahb_byte_strobe),

                          .sclk_out(sclk_out),
                          .sclk_negedge(sclk_negedge),
                          .sclk_sampling(sclk_sampling),
                          .sclk_sampling_en(sclk_sampling_en)
                      );

    wire SWCLK_TCK_O;
    wire SWDIO_TMS_O;
    wire SWDIO_TMS_T;
    reg SWDIO_TMS_I;
    wire [9:0] ram_write_addr;
    wire [7:0] ram_write_data;
    wire ram_write_en;
    wire [9:0] packet_len;

    DAP_SWJ #(12, 12'h080)
            inst(
                .clk(clk),
                .resetn(resetn),
                .clk_timer(timestamp),
                .enable(1'd1),

                //串行时钟
                .sclk(clk_x2),
                .sclk_out(sclk_out),
                .sclk_negedge(sclk_negedge),
                .sclk_sampling(sclk_sampling),
                .sclk_sampling_en(sclk_sampling_en),

                //AHBMEM接口
                .ahb_write_en(ahb_write_en),
                .ahb_read_en(ahb_read_en),
                .ahb_addr(ahb_addr),
                .ahb_rdata(),
                .ahb_wdata(ahb_wdata),
                .ahb_byte_strobe(ahb_byte_strobe),

                .dap_in_tvalid(dap_in_tvalid),
                .dap_in_tready(dap_in_tready[`CMD_SWJ_RANGE]),
                .dap_in_tdata(dap_in_tdata),

                .ram_write_addr(ram_write_addr),
                .ram_write_data(ram_write_data),
                .ram_write_en(ram_write_en),
                .packet_len(packet_len),

                .start(start[`CMD_SWJ_RANGE]),
                .done(done[`CMD_SWJ_RANGE]),

                .SWCLK_TCK_O(SWCLK_TCK_O),
                .SWDIO_TMS_T(SWDIO_TMS_T),
                .SWDIO_TMS_O(SWDIO_TMS_O),
                .SWDIO_TMS_I(SWDIO_TMS_I),
                .SWO_TDO_I(),
                .TDI_O(),
                //.RTCK_I,
                .SRST_I(),
                .SRST_O(),
                .TRST_I(),
                .TRST_O(),

                //swd模式信号
                .SWD_MODE()
            );


    reg [7:0] output_data [0:1023];

    always @(posedge clk) begin
        if (ram_write_en) begin
            output_data[ram_write_addr] <= ram_write_data;
            $display("write %08x %02x", ram_write_addr, ram_write_data);
        end


    end

    localparam [3:0] SWD_TRANS_IO_START = 4'd0;
    localparam [3:0] SWD_TRANS_IO_APnDP = 4'd1;
    localparam [3:0] SWD_TRANS_IO_RnW = 4'd2;
    localparam [3:0] SWD_TRANS_IO_A2 = 4'd3;
    localparam [3:0] SWD_TRANS_IO_A3 = 4'd4;
    localparam [3:0] SWD_TRANS_IO_PARITY = 4'd5;
    localparam [3:0] SWD_TRANS_IO_STOP = 4'd6;
    localparam [3:0] SWD_TRANS_IO_PARK = 4'd7;
    localparam [3:0] SWD_TRANS_IO_TURN1 = 4'd8;
    localparam [3:0] SWD_TRANS_IO_ACK0 = 4'd9;
    localparam [3:0] SWD_TRANS_IO_ACK1  = 4'd10;
    localparam [3:0] SWD_TRANS_IO_ACK2 = 4'd11;
    localparam [3:0] SWD_TRANS_IO_TURN2 = 4'd12;
    localparam [3:0] SWD_TRANS_IO_DATA = 4'd13;
    localparam [3:0] SWD_TRANS_IO_DATA_PATIYY = 4'd14;
    localparam [3:0] SWD_TRANS_IO_DONE = 4'd15;


    reg [7:0] swd_sm;
    reg APnDP;
    reg RnW;
    reg [3:0] Addr;
    reg Parity;
    reg [31:0] data;
    reg [7:0] data_cnt;
    reg DataParity;
    reg [2:0] tx_ack;
    reg [11:0] turn_cnt;

    initial begin
        SWDIO_TMS_I = 0;
        swd_sm = 0;
        APnDP = 0;
        RnW = 0;
        Addr = 0;
        Parity = 0;
        data = 32'h12345678;
        DataParity = 0;
        turn_cnt = 0;
        tx_ack = 3'b001;
        // tx_ack = 3'b010;
        // tx_ack = 3'b100;
    end

    wire swdio_i = SWDIO_TMS_O;

    always @(posedge SWCLK_TCK_O) begin
        case (swd_sm)
            SWD_TRANS_IO_START: begin
                DataParity <= 0;
                if (swdio_i) begin
                    swd_sm <= swd_sm + 1;
                end
            end
            SWD_TRANS_IO_APnDP: begin
                APnDP <= swdio_i;
                swd_sm <= swd_sm + 1;
            end
            SWD_TRANS_IO_RnW: begin
                RnW <= swdio_i;
                swd_sm <= swd_sm + 1;
            end
            SWD_TRANS_IO_A2: begin
                Addr[2] <= swdio_i;
                swd_sm <= swd_sm + 1;
            end
            SWD_TRANS_IO_A3: begin
                Addr[3] <= swdio_i;
                swd_sm <= swd_sm + 1;
            end
            SWD_TRANS_IO_PARITY: begin
                Parity <= swdio_i;
                swd_sm <= swd_sm + 1;
            end
            SWD_TRANS_IO_STOP, SWD_TRANS_IO_PARK: begin // stop, park, tm
                swd_sm <= swd_sm + 1;
            end
            SWD_TRANS_IO_TURN1: begin
                if (turn_cnt == `TRUN_CYCLE) begin
                    turn_cnt <= 12'd0;
                    SWDIO_TMS_I <= #`DELAY_TIME tx_ack[0];
                    swd_sm <= SWD_TRANS_IO_ACK0;
                end
                else begin
                    turn_cnt <= turn_cnt + 1'd1;
                end
            end
            SWD_TRANS_IO_ACK0: begin // ack 0
                SWDIO_TMS_I <= #`DELAY_TIME tx_ack[1];
                swd_sm <= swd_sm + 1;
            end
            SWD_TRANS_IO_ACK1: begin // ack 1
                SWDIO_TMS_I <= #`DELAY_TIME tx_ack[2];
                swd_sm <= swd_sm + 1;
            end
            SWD_TRANS_IO_ACK2: begin // ack 2
                // SWDIO_TMS_I <= #`DELAY_TIME tx_ack[2];

                if (tx_ack == 3'b001) begin
                    // 读请求ACK后跟数据段
                    // 写请求ACK后跟TURN
                    if (RnW) begin
                        data_cnt <= 1;
                        SWDIO_TMS_I <= #`DELAY_TIME data[0];
                        swd_sm <= SWD_TRANS_IO_DATA;
                    end
                    else begin
                        data_cnt <= 0;
                        swd_sm <= SWD_TRANS_IO_TURN2;
                    end
                end
                else begin
                    swd_sm <= SWD_TRANS_IO_TURN2;
                    tx_ack <= RnW ? 3'b001 : tx_ack;
                end
            end
            SWD_TRANS_IO_TURN2: begin // turn
                if (turn_cnt == `TRUN_CYCLE) begin
                    turn_cnt <= 12'd0;

                    SWDIO_TMS_I <= #`DELAY_TIME 1'd0;
                    if (tx_ack == 3'b001) begin
                        // 读请求TURN2位于末尾，转到结束
                        // 写请求位于数据段前，转到数据段
                        swd_sm <= RnW ? SWD_TRANS_IO_START : SWD_TRANS_IO_DATA;
                    end
                    else begin
                        swd_sm <= SWD_TRANS_IO_START;
                        tx_ack <= 3'b001;
                    end
                end
                else begin
                    turn_cnt <= turn_cnt + 1'd1;
                end


            end
            SWD_TRANS_IO_DATA: begin // data
                data_cnt <= data_cnt + 1;
                if (data_cnt == 31) begin
                    SWDIO_TMS_I <= #`DELAY_TIME parity_32(data);
                    swd_sm <= SWD_TRANS_IO_DATA_PATIYY;
                end
                if (RnW) begin
                    SWDIO_TMS_I <= #`DELAY_TIME data[data_cnt];
                end
                else begin
                    data[data_cnt] <= SWDIO_TMS_O;
                end
            end
            SWD_TRANS_IO_DATA_PATIYY: begin // p
                SWDIO_TMS_I <= #`DELAY_TIME parity_32(data);
                DataParity = (parity_32(data) == swdio_i);
                swd_sm <= RnW ? SWD_TRANS_IO_TURN2 : SWD_TRANS_IO_START;
            end
        endcase
    end

    function parity_32;
        input [31:0] data;
        begin
            parity_32 =
                data[ 0] ^ data[ 1] ^ data[ 2] ^ data[ 3] ^ data[ 4] ^ data[ 5] ^ data[ 6] ^ data[ 7] ^
                data[ 8] ^ data[ 9] ^ data[10] ^ data[11] ^ data[12] ^ data[13] ^ data[14] ^ data[15] ^
                data[16] ^ data[17] ^ data[18] ^ data[19] ^ data[20] ^ data[21] ^ data[22] ^ data[23] ^
                data[24] ^ data[25] ^ data[26] ^ data[27] ^ data[28] ^ data[29] ^ data[30] ^ data[31];
        end
    endfunction
endmodule
