LX050724/HFLink/MCU/Firmware/drivers/inc/GOWIN_M1_qspi_flash.h

/*
 **************************************************************************************************
 * @file      GOWIN_M1_qspi_flash.h
 * @author    GowinSemicoductor
 * @device    Gowin_EMPU_M1
 * @brief     This file contains all the functions prototypes for the QSPI-Flash firmware library.
 **************************************************************************************************
 */

/* Define to prevent recursive inclusion -------------------------------------*/
#ifndef GOWIN_M1_QSPI_FLASH_H
#define GOWIN_M1_QSPI_FLASH_H

#ifdef __cplusplus
 extern "C" {
#endif

/* Includes ------------------------------------------------------------------*/
#include "stdint.h"
#include "GOWIN_M1.h"

/** @addtogroup GOWIN_M1_StdPeriph_Driver
  * @{
  */
/** @addtogroup QSPI_FLASH
  * @{
  */

/* Macros ------------------------------------------------------------------*/
#define SPI_CMDEN                     (1UL << 30)
#define SPI_ADDREN                    (1UL << 29)

//The winbone qspi-flash command
#define WRITE_CMD													0x01	//write
#define	PROGRAM_CMD												0x02	//page program
#define READ_CMD													0x03	//read
#define WRITE_DISABLE_CMD                 0x04	//disable write
#define READ_STATUS_CMD										0x05	//read status
#define WRITE_ENABLE_CMD                  0x06	//enable write
#define	ERASE_4K_CMD											0x20	//erase 4k
#define ERASE_32K_CMD											0x52	//erase 32k
#define ERASE_64K_CMD											0xD8	//erase 64k
#define ERASE_CHIP_CMD                    0x60  //erase full chip

#define DUAL_FAST_READ_CMD                0x3B  //fast read dual output

#define QUAD_PROGRAM_CMD                  0x32  //quad page program
#define QUAD_FAST_READ_CMD                0x6B  //fast read quad output
#define QUAD_IO_FAST_READ_CMD             0xEB  //I/O fast read quad output

#define ENTER_QSPI_MODE_CMD      					0x38	//enable qspi mode
#define EXIT_QSPI_MODE_CMD      					0xFF	//disable qspi mode

#define READ_STATUS_REG1_CMD							0x05 
#define READ_STATUS_REG2_CMD							0x35 
#define READ_STATUS_REG3_CMD							0x15 
#define WRITE_STATUS_REG1_CMD    					0x01 
#define WRITE_STATUS_REG2_CMD    					0x31 
#define WRITE_STATUS_REG3_CMD    					0x11 

#define QSPI_ADDRESS_8_BITS  (0x00000000U)
#define QSPI_ADDRESS_16_BITS ((uint32_t)SPIFLASH_TRANSFMT_ADSIZE_0)
#define QSPI_ADDRESS_24_BITS ((uint32_t)SPIFLASH_TRANSFMT_ADSIZE_1)
#define QSPI_ADDRESS_32_BITS ((uint32_t)SPIFLASH_TRANSFMT_ADSIZE)

#define QSPI_DATA_8_BITS ((uint32_t)(7 << SPIFLASH_TRANSFMT_DATAL_Pos))

#define QSPI_INSTRUCTION_NONE          0x00000000U                          /*!<No instruction*/
#define QSPI_INSTRUCTION_1_LINE        ((uint32_t)SPIFLASH_TRANSCTRL_CMDEN) /*!<Instruction on a single line*/

#define QSPI_DATA_1_LINE   (0x00000000U)
#define QSPI_DATA_2_LINES  ((uint32_t)SPIFLASH_TRANSCTRL_DATAFMT_0)
#define QSPI_DATA_4_LINES  ((uint32_t)SPIFLASH_TRANSCTRL_DATAFMT_1)

#define QSPI_ADDRESS_NONE      (0x00000000U)
#define QSPI_ADDRESS_1LINE     ((uint32_t)SPIFLASH_TRANSCTRL_ADREN)
#define QSPI_ADDRESS_SAME_DATA ((uint32_t)(SPIFLASH_TRANSCTRL_ADREN | SPIFLASH_TRANSCTRL_ADRMODE))

#define QSPI_TRMODE_WRITE_READ       ((uint32_t)(0x0UL << SPIFLASH_TRANSCTRL_TRMODE_Pos)) /* Write and read at same time */
#define QSPI_TRMODE_WRITE_ONLY       ((uint32_t)(0x1UL << SPIFLASH_TRANSCTRL_TRMODE_Pos))
#define QSPI_TRMODE_READ_ONLY        ((uint32_t)(0x2UL << SPIFLASH_TRANSCTRL_TRMODE_Pos))
#define QSPI_TRMODE_WRITE_COMMA_READ ((uint32_t)(0x3UL << SPIFLASH_TRANSCTRL_TRMODE_Pos)) /* Write, Read */
#define QSPI_TRMODE_READ_COMMA_WRITE ((uint32_t)(0x4UL << SPIFLASH_TRANSCTRL_TRMODE_Pos)) /* Read, Write */
#define QSPI_TRMODE_WRITE_DUMMY_READ ((uint32_t)(0x5UL << SPIFLASH_TRANSCTRL_TRMODE_Pos)) /* Write, Dummy, Read */
#define QSPI_TRMODE_READ_DUMMY_WRITE ((uint32_t)(0x6UL << SPIFLASH_TRANSCTRL_TRMODE_Pos)) /* Read, Dummy, Write */
#define QSPI_TRMODE_NONE_DATA        ((uint32_t)(0x7UL << SPIFLASH_TRANSCTRL_TRMODE_Pos)) /* None data */
#define QSPI_TRMODE_DUMMY_WRITE      ((uint32_t)(0x8UL << SPIFLASH_TRANSCTRL_TRMODE_Pos)) /* Dummy, Write */
#define QSPI_TRMODE_DUMMY_READ       ((uint32_t)(0x9UL << SPIFLASH_TRANSCTRL_TRMODE_Pos)) /* Dummy, Read */

#define QSPI_DUMMY_NUM(NUM) ((((NUM) - 1) << SPIFLASH_TRANSCTRL_DUMMYCNT_Pos) & SPIFLASH_TRANSCTRL_DUMMYCNT_Msk)
#define QSPI_DATA_WRITE_TRANSMIT_NUM(NUM) ((((NUM) - 1) << SPIFLASH_TRANSCTRL_WRDT_CNT_Pos) & SPIFLASH_TRANSCTRL_WRDT_CNT_Msk)
#define QSPI_DATA_READ_TRANSMIT_NUM(NUM) ((((NUM) - 1) << SPIFLASH_TRANSCTRL_RDDT_CNT_Pos) & SPIFLASH_TRANSCTRL_RDDT_CNT_Msk)


/* Functions ------------------------------------------------------------------*/
/**
  * @brief Initializes QSPI-Flash
  */
extern void qspi_flash_init(void);

/**
  * @brief Switch QSPI-Flash mode between download and read/write/erase memory
  */
extern void change_mode_qspi_flash(void);

/**
  * @brief Write data into a page of QSPI-Flash
  */
extern void qspi_flash_page_program(uint16_t wr_len,uint32_t address,uint8_t *buffer);

/**
  * @brief Erase a 4K sector of QSPI-Flash
  */
extern void qspi_flash_4ksector_erase(uint32_t address);
void qspi_flash_32ksector_erase(uint32_t address);

/**
  * @brief Erase a 64K sector of QSPI-Flash
  */
extern void qspi_flash_64ksector_erase(uint32_t address);

/**
  * @brief Erase a full chip of QSPI-Flash
  */
extern void qspi_flash_chip_erase(void);

/**
  * @brief Write status register of QSPI-Flash
  */
extern void qspi_flash_write_sr(uint8_t reg, uint8_t byte);

/**
  * @brief Read status register of QSPI-Flash
  */
extern uint8_t qspi_flash_read_sr(uint8_t reg);

/**
  * @brief Enable QSPI-Flash
  */
extern void qspi_flash_Enable(void);
void qspi_flash_write_enable(void);
void qspi_flash_write_disable(void);
void qspi_flash_fast_read_quad(uint32_t address, uint8_t *read_buffer, uint16_t rd_len);
uint8_t qspi_flash_chip_reset();
uint8_t qspi_flash_read_status(void);
uint8_t qspi_flash_read_unique_id(uint8_t *write_buffer);
int qspi_flash_is_busy(void);

#ifdef __cplusplus
}
#endif

#endif	/* GOWIN_M1_QSPI_FLASH_H */

/**
  * @}
  */ 

/**
  * @}
  */
