LX050724/HFLink/FPGA/src/DAP_Controller/cmd_worker/DAP_Delay.v

`timescale 1 ns / 10 ps

module DAP_Delay #(
        parameter [5:0] CLOCK_FREQ_M = 60
    )(
        input clk,       // clock
        input resetn,
        input enable,
        input start,

        input wire dap_in_tvalid,
        output wire dap_in_tready,
        input wire [7:0] dap_in_tdata,

        output [9:0] ram_write_addr,
        output [7:0] ram_write_data,
        output ram_write_en,
        output [9:0] packet_len,

        output done
    );

    // reg [31:0] us_timer;  // us定时器
    reg [ 5:0] us_timer_div;
    wire us_tick = us_timer_div == (CLOCK_FREQ_M - 6'd1);

    reg [15:0] delay_time;
    reg delay_rx_tready;
    reg delay_tx_tvalid;
    reg delay_tx_tdata;
    reg [1:0] delay_sm;
    always @(posedge clk or negedge resetn) begin
        if (!enable || !resetn) begin
            delay_time <= 1'd0;
            delay_sm <= 2'd0;
            delay_tx_tvalid <= 1'd0;
            delay_tx_tdata <= 8'd0;
            us_timer_div <= 6'd0;
        end
        else begin
            if (start) begin
                case (delay_sm)
                    2'd0: // 收1
                        if (dap_in_tvalid) begin
                            delay_time[7:0] <= dap_in_tdata;
                            delay_sm <= 2'd1;
                        end
                    2'd1: // 收2
                        if (dap_in_tvalid) begin
                            delay_time[15:8] <= dap_in_tdata;
                            delay_sm <= 2'd2;
                        end
                    2'd2: begin// delay
                        if (us_tick) begin
                            us_timer_div <= 6'd0;
                        end
                        else begin
                            us_timer_div <= us_timer_div + 1;
                        end

                        if (us_tick) begin
                            delay_time <= delay_time - 16'd1;
                            if ((delay_time - 16'd1) == 16'd0) begin
                                // 发OK
                                delay_sm <= 2'd3;
                                delay_tx_tvalid <= 1'd1;
                                delay_tx_tdata <= 8'h00;
                            end
                        end
                    end
                    2'd3: begin
                        delay_tx_tvalid <= 1'd0;
                        delay_tx_tdata <= 8'h00;
                    end
                endcase
            end
            else begin
                // 复位
                delay_sm <= 2'd0;
            end
        end
    end

    assign done = (delay_sm == 2'd3);
    assign dap_in_tready = enable & (delay_sm == 2'd0 || delay_sm == 2'd1);

    assign ram_write_addr = 9'd0;
    assign ram_write_en = delay_tx_tvalid;
    assign ram_write_data = delay_tx_tdata;
    assign packet_len = 9'd1;
endmodule
