LX050724/HFLink/FPGA/src/DAP_Controller/DAP_Cmd.v

`define CMD_REG_WIDTH               13
`define CMD_REAL_NUM                (`CMD_REG_WIDTH-2)
`define CMD_SWJ_RANGE               `CMD_REAL_NUM-1:2

/* Controller处理命令 */
`define CMD_MCU_HELPER_SHIFT        0
`define CMD_MCU_HELPER              13'b?_????_????_???1

`define CMD_DELAY_SHIFT             1
`define CMD_DELAY                   13'b?_????_????_??1?
/* SWJ处理命令 */
`define CMD_TRANSFER_BLOCK_SHIFT    2
`define CMD_TRANSFER_BLOCK          13'b?_????_????_?1??

`define CMD_TRANSFER_SHIFT          3
`define CMD_TRANSFER                13'b?_????_????_1???

`define CMD_WRITE_ABORT_SHIFT       4
`define CMD_WRITE_ABORT             13'b?_????_???1_????

`define CMD_SWJ_PINS_SHIFT          5
`define CMD_SWJ_PINS                13'b?_????_??1?_????

`define CMD_SWJ_SEQUENCE_SHIFT      6
`define CMD_SWJ_SEQUENCE            13'b?_????_?1??_????

`define CMD_SWD_SEQUENCE_SHIFT      7
`define CMD_SWD_SEQUENCE            13'b?_????_1???_????

`define CMD_JTAG_SEQUENCE_SHIFT     8
`define CMD_JTAG_SEQUENCE           13'b?_???1_????_????

`define CMD_JTAG_IDCODE_SHIFT       9
`define CMD_JTAG_IDCODE             13'b?_??1?_????_????

`define CMD_SWO_STATUS_SHIFT        10
`define CMD_SWO_STATUS              13'b?_?1??_????_????
/* 不处理命令 */
`define CMD_TRANSFER_ABORT_SHIFT    11
`define CMD_TRANSFER_ABORT          13'b?_1???_????_????
/* 虚命令 */
`define CMD_EXEC_CMD_SHIFT          12
`define CMD_EXEC_CMD                13'b1_????_????_????


/**
 * SWD_Sequence
 * | 15 14 13 12 | 11 10  9  8  7  6  5 |    4 |       3  2  1  0 |
 * |  0  0  0  0 |  x  x  x  x  x  x  x | mode | Number of cycles |
 * mode 0: output; 1: input
 * Number of cycles [1-8]
 */
`define SEQ_CMD_SWD_SEQ             4'd0
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
